Danjovic/AT26-Chuck/Doc/AT26-JoyTest-sch.png.jpg

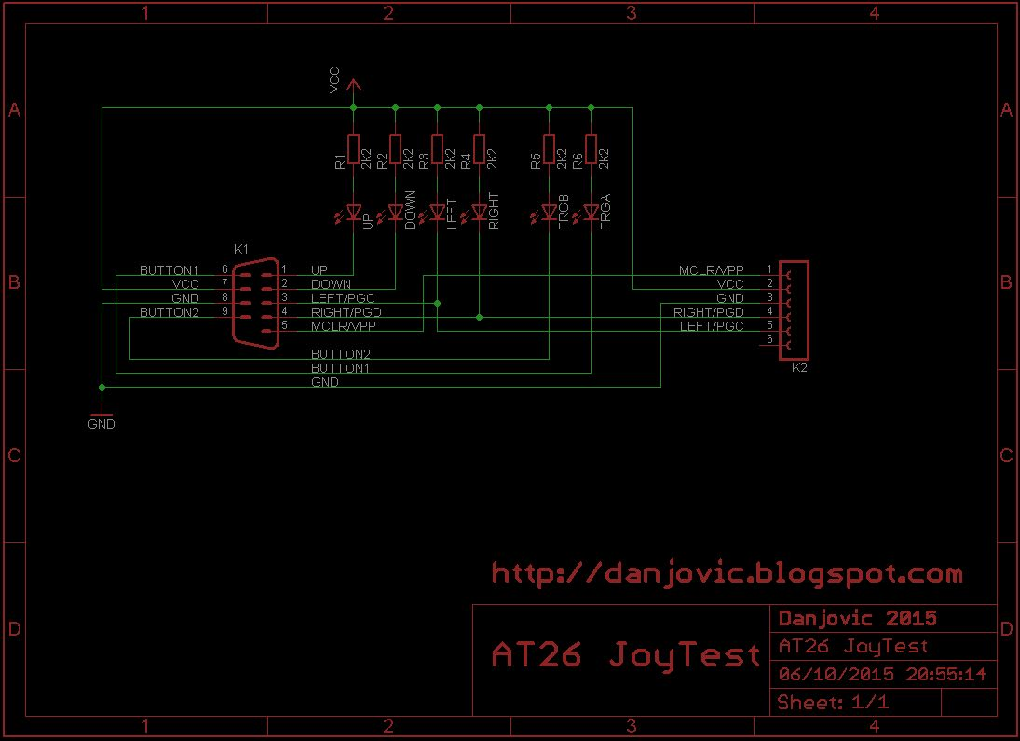
Doc/AT26-JoyTest-sch.png.jpg
